luka1983/beer_tc/firmware/src/serial.c

#include <string.h>
#include <stdarg.h>
#include <stdio.h>
#include <avr/io.h>
#include <avr/interrupt.h>
#include "serial.h"
#include "commands.h"

static uint8_t terminal_mode = 1;

void init_serial(uint16_t brate, uint8_t dbits, uint8_t parity, uint8_t sbits) {
	uint16_t ubrr0 = (uint16_t) (F_CPU / (brate * 16UL)) - 1;
	UBRR0H = (uint8_t)(ubrr0 >> 8);				// configure baud rate
	UBRR0L = (uint8_t)(ubrr0);
	UCSR0C |= (1 << UCSZ01) | (1 << UCSZ00);	// configure data bits, parity and stop bits
	UCSR0B |= (1 << RXEN0) | (1 << TXEN0);		// enable RX/TX
	UCSR0B |= (1 << RXCIE0);					// enable interrupt on RX
}

void crnl() {
	sputc('\r');
	sputc('\n');
}

void sputc(const char c) {
	while (!(UCSR0A & (1<<UDRE0)));
	UDR0 = c;
}

void sprints(const char* fmt, ...) {
	char str[MAX_SLEN];
	char* p = &str[0];
	va_list args;
	va_start(args, fmt);
	vsprintf(str, fmt, args);
	va_end(args);
	while (*p != '\0')
		sputc(*(p++));
}

ISR(USART_RX_vect) {
	uint8_t rb = UDR0;
	static char res[MAX_SLEN];

	if (terminal_mode) {
		sputc(rb);
		if (rb == '\r')
			sputc('\n');
	}

	strcpy(res, update_command_buffer(rb));

	if (res[0] != '\0') {
		sprints(res);
		if (terminal_mode) crnl();
	}
}
